minfia/dso138-sub-system/src/dso138_sub_system/system.h

/**
 * @file    system.h
 * @brief   システムの設定を定義
 *
 * @author  minfia
 * @note
 *  Fuse bit設定<br>
 *    EXTENDED: 0xF9<br>
 *    HIGH:     0xDC<br>
 *    LOW:      0xE2<br>
 */


#ifndef INCLUDE_GUARD_UUID_D46226AC_FF88_45B6_BF93_2FA7615682A2
#define INCLUDE_GUARD_UUID_D46226AC_FF88_45B6_BF93_2FA7615682A2


#ifdef __cplusplus
extern "C" {
#endif /* __cplusplus */


#define VERSION "1.0.0"
#define VERSION_BCD 0x100
#define PROGRAM "DSO138 Sub System"


#ifdef __cplusplus
}
#endif /* __cplusplus */
#endif /* INCLUDE_GUARD_UUID_D46226AC_FF88_45B6_BF93_2FA7615682A2 */
